Tinkerforge/warp-energy-manager-bricklet/software/src/io.c

/* hat-warp-energy-manager-brick
 * Copyright (C) 2021 Olaf Lüke <olaf@tinkerforge.com>
 *
 * io.c: Driver for IO
 *
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
 * You should have received a copy of the GNU Lesser General Public
 * License along with this library; if not, write to the
 * Free Software Foundation, Inc., 59 Temple Place - Suite 330,
 * Boston, MA 02111-1307, USA.
 */

#include "io.h"

#include "configs/config_io.h"

#include "xmc_gpio.h"

#include "bricklib2/hal/system_timer/system_timer.h"
#include "bricklib2/logging/logging.h"

IO io;

bool io_get_contactor_check(void) {
	// Don't do contactor check if contact state changed recently
	if(io.contactor_change_time != 0) {
		return true;
	}

	// Contactor pin active low, contactor check pin active low
	const bool contactor_ok = XMC_GPIO_GetInput(IO_CONTACTOR_PIN) == XMC_GPIO_GetInput(IO_INPUT1_PIN);

	// Check if contactor failed and add a debounce time of 5ms
	if(!contactor_ok && !io.contactor_fail) {
		io.contactor_fail = true;
		io.contactor_fail_time = system_timer_get_ms();
	} else if(!contactor_ok && io.contactor_fail) {
		if(system_timer_is_time_elapsed_ms(io.contactor_fail_time, 5)) {
			return false;
		}
	} else {
		io.contactor_fail = false;
		io.contactor_fail_time = 0;
	}

	return true;
}

void io_init(void) {
	memset(&io, 0, sizeof(IO));
	const XMC_GPIO_CONFIG_t io_config_high = {
		.mode             = XMC_GPIO_MODE_OUTPUT_PUSH_PULL,
		.output_level     = XMC_GPIO_OUTPUT_LEVEL_HIGH,
	};

	const XMC_GPIO_CONFIG_t io_config_low = {
		.mode             = XMC_GPIO_MODE_OUTPUT_PUSH_PULL,
		.output_level     = XMC_GPIO_OUTPUT_LEVEL_LOW,
	};

	const XMC_GPIO_CONFIG_t io_config_input = {
		.mode             = XMC_GPIO_MODE_INPUT_TRISTATE,
		.input_hysteresis = XMC_GPIO_INPUT_HYSTERESIS_LARGE,
	};

	XMC_GPIO_Init(IO_CONTACTOR_PIN, &io_config_high);
	XMC_GPIO_Init(IO_OUTPUT_PIN, &io_config_low);

	XMC_GPIO_Init(IO_INPUT0_PIN, &io_config_input);
	XMC_GPIO_Init(IO_INPUT1_PIN, &io_config_input);
}

void io_tick(void) {
	if(system_timer_is_time_elapsed_ms(io.contactor_change_time, IO_CONTACTOR_CHANGE_WAIT_TIME)) {
		io.contactor_change_time = 0;
	}

	if(XMC_GPIO_GetInput(IO_CONTACTOR_PIN) == io.contactor) {
		io.contactor_change_time = system_timer_get_ms();
	}

	if(io.contactor) { // Active low
		XMC_GPIO_SetOutputLow(IO_CONTACTOR_PIN);
	} else {
		XMC_GPIO_SetOutputHigh(IO_CONTACTOR_PIN);
	}

	if(io.output) { // Active high
		XMC_GPIO_SetOutputHigh(IO_OUTPUT_PIN);
	} else {
		XMC_GPIO_SetOutputLow(IO_OUTPUT_PIN);
	}

	io.input[0] = !XMC_GPIO_GetInput(IO_INPUT0_PIN);
	io.input[1] = !XMC_GPIO_GetInput(IO_INPUT1_PIN);

	// Ignore contactor check output here, we just call this to update the time
	io_get_contactor_check();
}
